BleepSound/ms20-vcf-double/documentation/image/MS20-VCF-3D_top.png

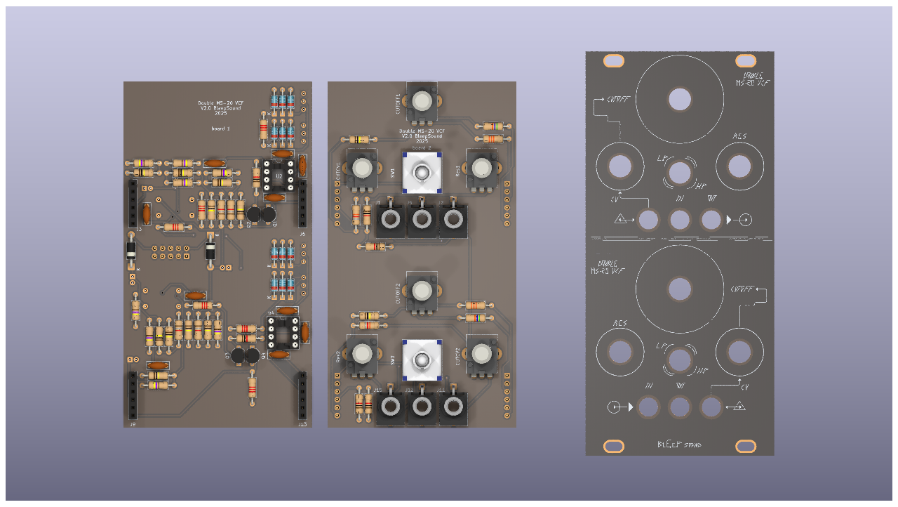
documentation/image/MS20-VCF-3D_top.png
