BleepSound/ms20-vcf-double/documentation/image/MS20-VCF-top.png

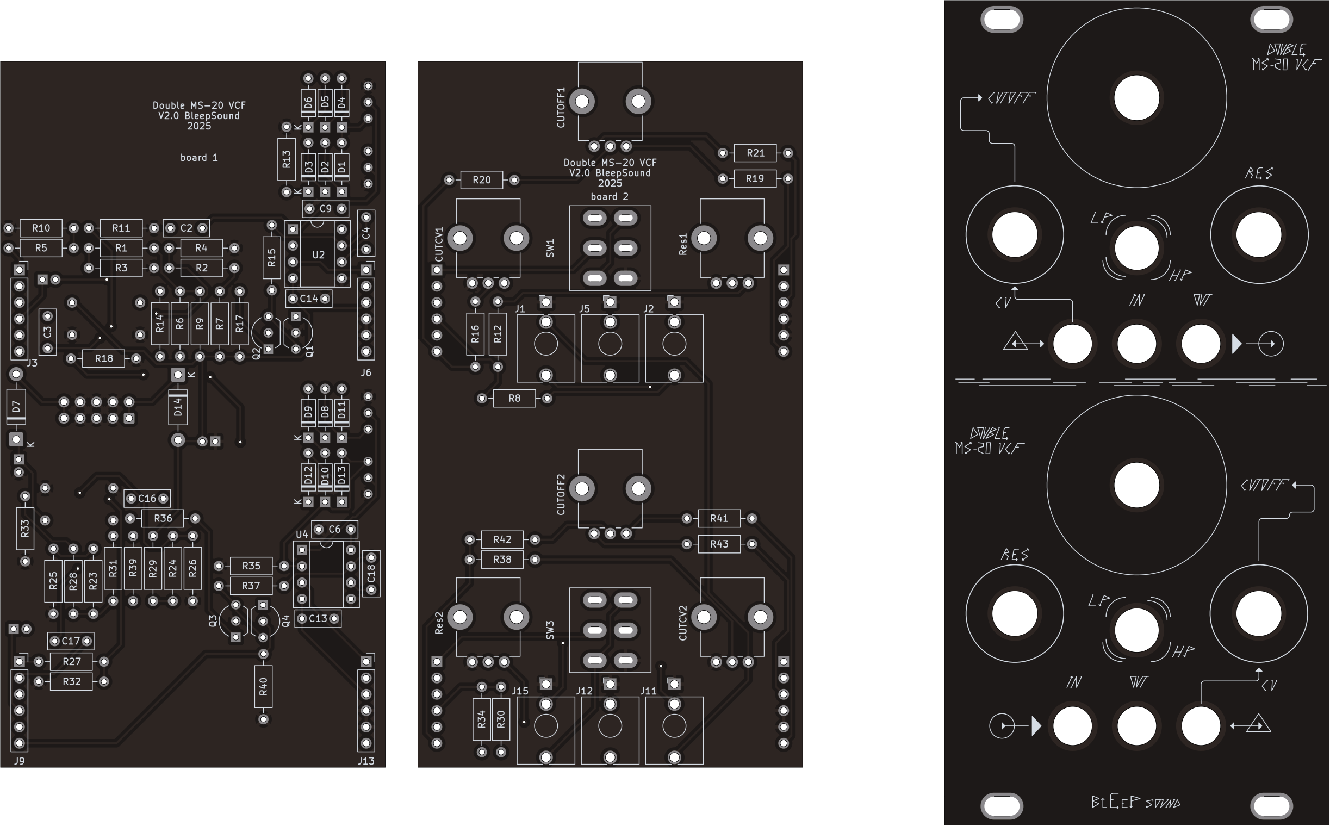
documentation/image/MS20-VCF-top.png
